tducret/programmateur-fil-pilote-wifi/Matériel/1.0/ProgrammateurFilPilote_1.0_Recto.png

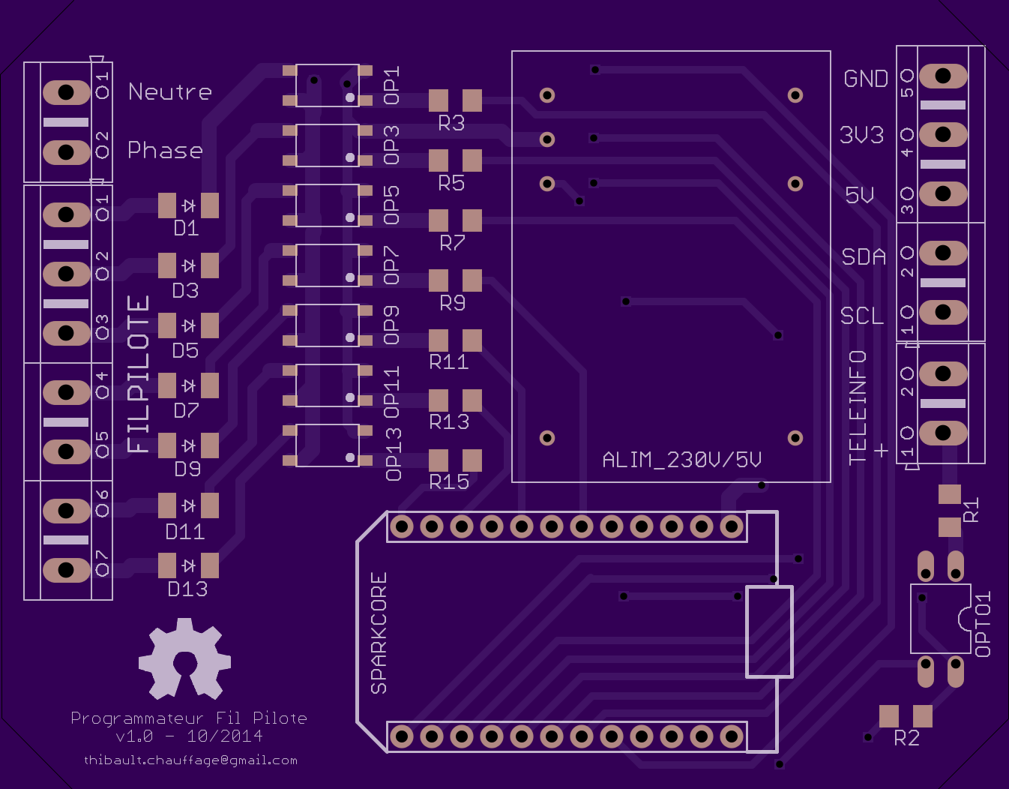
Matériel/1.0/ProgrammateurFilPilote_1.0_Recto.png
