tducret/programmateur-fil-pilote-wifi/Matériel/1.0/ProgrammateurFilPilote_1.0_Verso.png

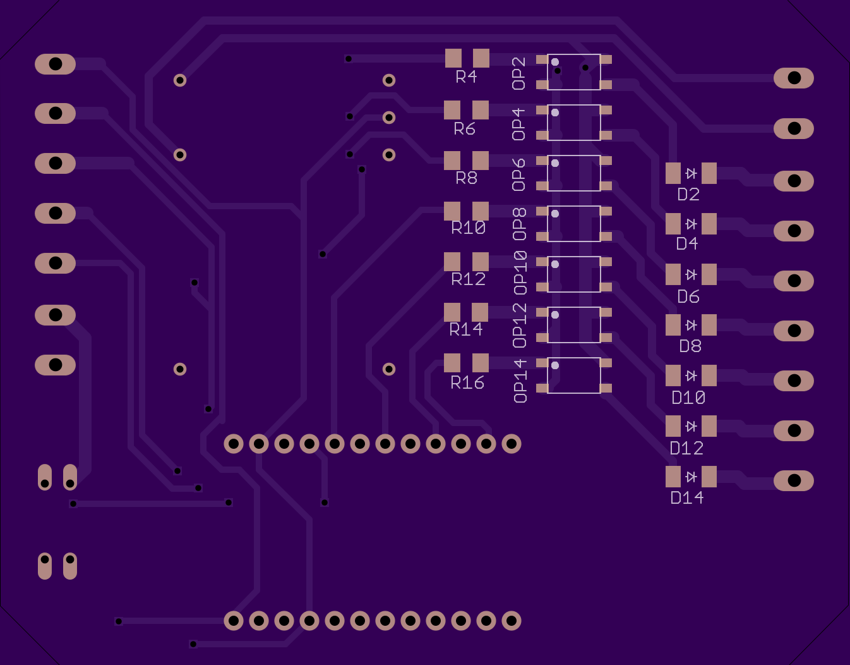
Matériel/1.0/ProgrammateurFilPilote_1.0_Verso.png
