tducret/programmateur-fil-pilote-wifi/Matériel/1.1.1/ProgrammateurFilPilote_1.1.1_Verso.png

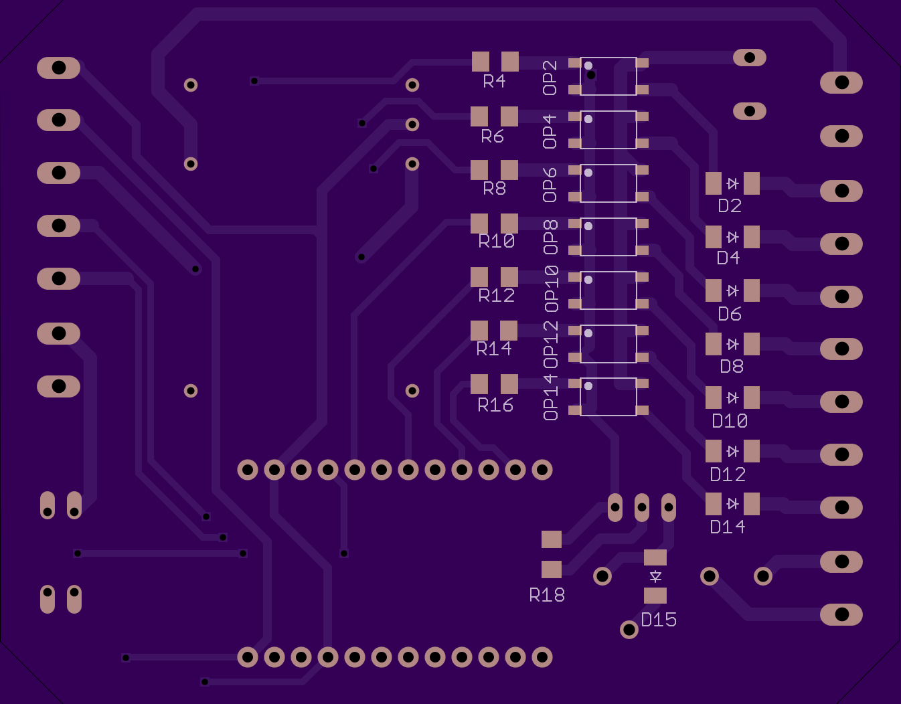
Matériel/1.1.1/ProgrammateurFilPilote_1.1.1_Verso.png
