tducret/programmateur-fil-pilote-wifi/Matériel/1.2/ProgrammateurFilPilote_1.2_Board.png

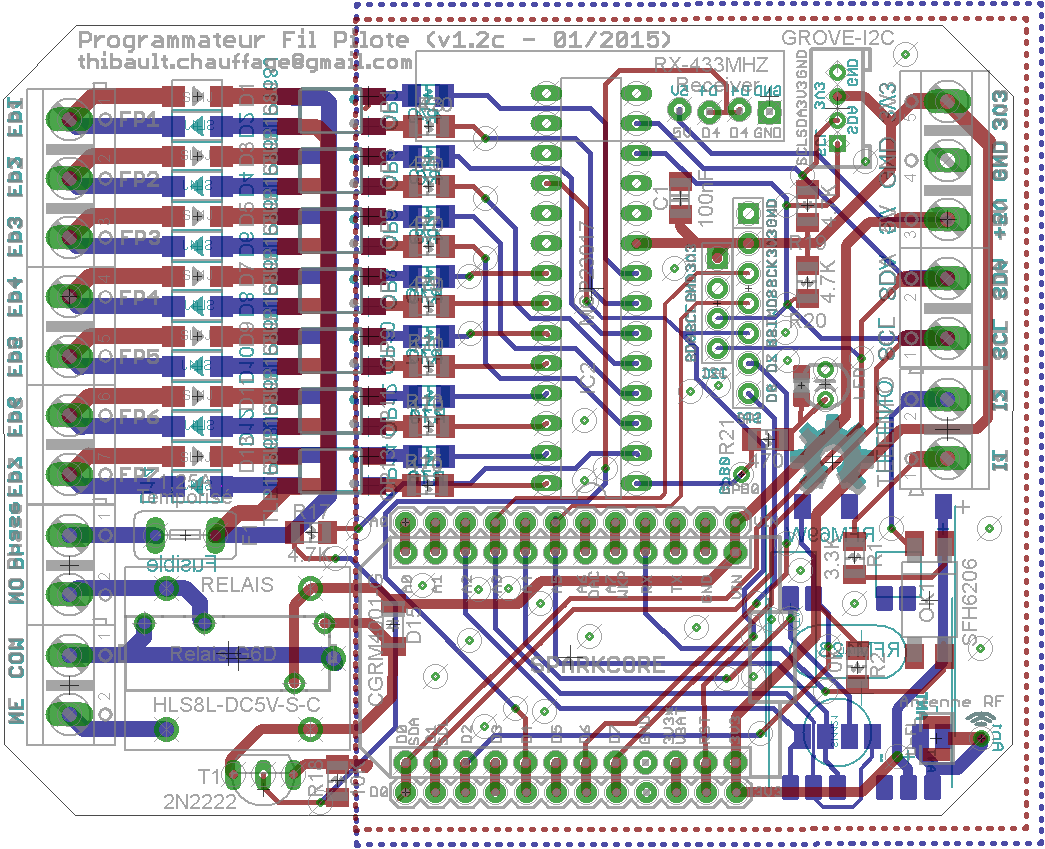
Matériel/1.2/ProgrammateurFilPilote_1.2_Board.png
