tducret/programmateur-fil-pilote-wifi/Matériel/1.2/ProgrammateurFilPilote_1.2_Recto.png

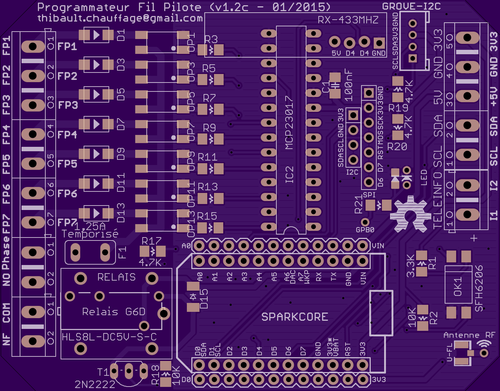
Matériel/1.2/ProgrammateurFilPilote_1.2_Recto.png
