tducret/programmateur-fil-pilote-wifi/Matériel/1.2/ProgrammateurFilPilote_1.2_Verso.png

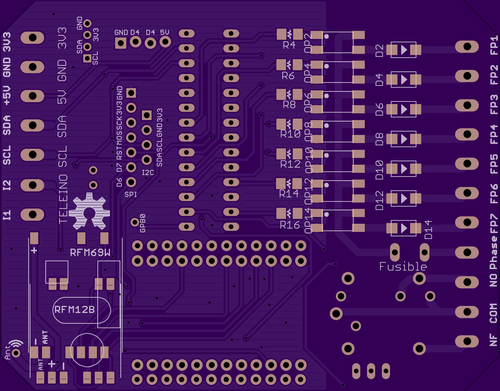
Matériel/1.2/ProgrammateurFilPilote_1.2_Verso.png
