tducret/programmateur-fil-pilote-wifi/Matériel/1.3/ProgrammateurFilPilote_1.3_Verso.png

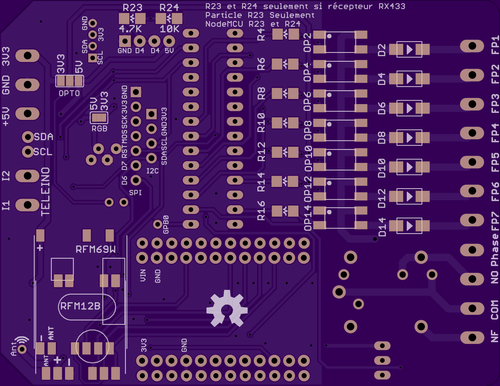
Matériel/1.3/ProgrammateurFilPilote_1.3_Verso.png
