tducret/programmateur-fil-pilote-wifi/Matériel/1.3/Tutoriel/Images/Photo16.jpeg

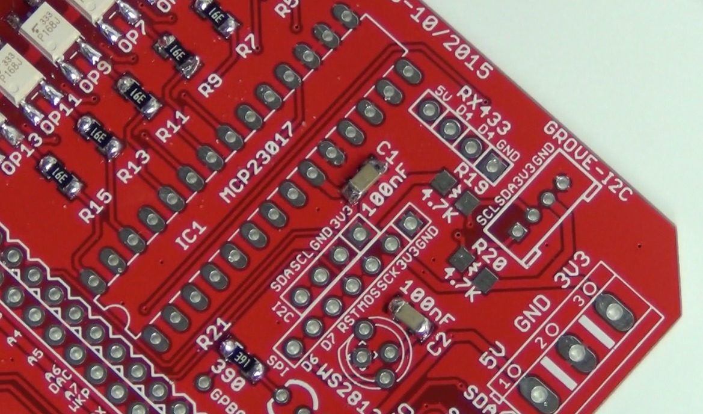
Matériel/1.3/Tutoriel/Images/Photo16.jpeg
