tducret/programmateur-fil-pilote-wifi/Logiciel/remora/WebServer/WebServer.h

/* -*- Mode: C++; tab-width: 2; indent-tabs-mode: nil;  c-file-style: "k&r"; c-basic-offset: 2; -*-

   Webduino, a simple Arduino web server
   Copyright 2009-2014 Ben Combee, Ran Talbott, Christopher Lee, Martin Lormes
   Francisco M Cuenca-Acuna, Matthew McGowan

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
   THE SOFTWARE IS PROVIDED "AS IS", WITHOUT WARRANTY OF ANY KIND, EXPRESS OR
   IMPLIED, INCLUDING BUT NOT LIMITED TO THE WARRANTIES OF MERCHANTABILITY,
   FITNESS FOR A PARTICULAR PURPOSE AND NONINFRINGEMENT. IN NO EVENT SHALL THE
   AUTHORS OR COPYRIGHT HOLDERS BE LIABLE FOR ANY CLAIM, DAMAGES OR OTHER
   LIABILITY, WHETHER IN AN ACTION OF CONTRACT, TORT OR OTHERWISE, ARISING FROM,
   OUT OF OR IN CONNECTION WITH THE SOFTWARE OR THE USE OR OTHER DEALINGS IN
   THE SOFTWARE.
*/

#ifndef WEBDUINO_H_
#define WEBDUINO_H_

#include <string.h>
#include <stdlib.h>
#include <stdarg.h>
#include "remora.h"

// TODO - this is necessary to avoid sockets being unexpectedly closed.
// https://community.spark.io/t/unwanted-but-reproducable-disconnect-in-tcpclient/5265
#define fixmedelay() delay(20)

/********************************************************************
 * CONFIGURATION
 ********************************************************************/

#define WEBDUINO_VERSION 1007
#define WEBDUINO_VERSION_STRING "1.7"

// standard END-OF-LINE marker in HTTP
#define CRLF "\r\n"

// If processConnection is called without a buffer, it allocates one
// of 32 bytes
#define WEBDUINO_DEFAULT_REQUEST_LENGTH 32

// How long to wait before considering a connection as dead when
// reading the HTTP request.  Used to avoid DOS attacks.
#ifndef WEBDUINO_READ_TIMEOUT_IN_MS
#define WEBDUINO_READ_TIMEOUT_IN_MS 1000
#endif

#ifndef WEBDUINO_COMMANDS_COUNT
#define WEBDUINO_COMMANDS_COUNT 8
#endif

#ifndef WEBDUINO_URL_PATH_COMMAND_LENGTH
#define WEBDUINO_URL_PATH_COMMAND_LENGTH 8
#endif

#ifndef WEBDUINO_FAIL_MESSAGE
#define WEBDUINO_FAIL_MESSAGE "<h1>EPIC FAIL</h1>"
#endif

#ifndef WEBDUINO_AUTH_REALM
#define WEBDUINO_AUTH_REALM "Webduino"
#endif // #ifndef WEBDUINO_AUTH_REALM

#ifndef WEBDUINO_AUTH_MESSAGE
#define WEBDUINO_AUTH_MESSAGE "<h1>401 Unauthorized</h1>"
#endif // #ifndef WEBDUINO_AUTH_MESSAGE

#ifndef WEBDUINO_SERVER_ERROR_MESSAGE
#define WEBDUINO_SERVER_ERROR_MESSAGE "<h1>500 Internal Server Error</h1>"
#endif // WEBDUINO_SERVER_ERROR_MESSAGE

#ifndef WEBDUINO_OUTPUT_BUFFER_SIZE
#define WEBDUINO_OUTPUT_BUFFER_SIZE 32
#endif // WEBDUINO_OUTPUT_BUFFER_SIZE

// add '#define WEBDUINO_FAVICON_DATA ""' to your application
// before including WebServer.h to send a null file as the favicon.ico file
// otherwise this defaults to a 16x16 px black diode on blue ground
// (or include your own icon if you like)
#ifndef WEBDUINO_FAVICON_DATA
#define WEBDUINO_FAVICON_DATA { 0x00, 0x00, 0x01, 0x00, 0x01, 0x00, 0x10, \
                                0x10, 0x02, 0x00, 0x01, 0x00, 0x01, 0x00, \
                                0xb0, 0x00, 0x00, 0x00, 0x16, 0x00, 0x00, \
                                0x00, 0x28, 0x00, 0x00, 0x00, 0x10, 0x00, \
                                0x00, 0x00, 0x20, 0x00, 0x00, 0x00, 0x01, \
                                0x00, 0x01, 0x00, 0x00, 0x00, 0x00, 0x00, \
                                0x00, 0x00, 0x00, 0x00, 0x00, 0x00, 0x00, \
                                0x00, 0x00, 0x00, 0x00, 0x00, 0x00, 0x00, \
                                0x00, 0x00, 0x00, 0x00, 0x00, 0x00, 0x00, \
                                0x00, 0x00, 0x00, 0xff, 0x00, 0x00, 0x00, \
                                0xff, 0xff, 0x00, 0x00, 0xff, 0xff, 0x00, \
                                0x00, 0xff, 0xff, 0x00, 0x00, 0xcf, 0xbf, \
                                0x00, 0x00, 0xc7, 0xbf, 0x00, 0x00, 0xc3, \
                                0xbf, 0x00, 0x00, 0xc1, 0xbf, 0x00, 0x00, \
                                0xc0, 0xbf, 0x00, 0x00, 0x00, 0x00, 0x00, \
                                0x00, 0xc0, 0xbf, 0x00, 0x00, 0xc1, 0xbf, \
                                0x00, 0x00, 0xc3, 0xbf, 0x00, 0x00, 0xc7, \
                                0xbf, 0x00, 0x00, 0xcf, 0xbf, 0x00, 0x00, \
                                0xff, 0xff, 0x00, 0x00, 0xff, 0xff, 0x00, \
                                0x00, 0x00, 0x00, 0x00, 0x00, 0x00, 0x00, \
                                0x00, 0x00, 0x00, 0x00, 0x00, 0x00, 0x00, \
                                0x00, 0x00, 0x00, 0x00, 0x00, 0x00, 0x00, \
                                0x00, 0x00, 0x00, 0x00, 0x00, 0x00, 0x00, \
                                0x00, 0x00, 0x00, 0x00, 0x00, 0x00, 0x00, \
                                0x00, 0x00, 0x00, 0x00, 0x00, 0x00, 0x00, \
                                0x00, 0x00, 0x00, 0x00, 0x00, 0x00, 0x00, \
                                0x00, 0x00, 0x00, 0x00, 0x00, 0x00, 0x00, \
                                0x00, 0x00, 0x00, 0x00, 0x00, 0x00, 0x00, \
                                0x00, 0x00 }
#endif // #ifndef WEBDUINO_FAVICON_DATA

// add "#define WEBDUINO_SERIAL_DEBUGGING 1" to your application
// before including WebServer.h to have incoming requests logged to
// the serial port.
#ifndef WEBDUINO_SERIAL_DEBUGGING
#define WEBDUINO_SERIAL_DEBUGGING 0
#endif
#if WEBDUINO_SERIAL_DEBUGGING
	#define SERIAL_DUMP(buf, len) Serial.write(buf, len);
#else
	#define SERIAL_DUMP(buf, len)
#endif

// declare a static string
#define P(name)   static const unsigned char name[]

// returns the number of elements in the array
#define SIZE(array) (sizeof(array) / sizeof(*array))

/********************************************************************
 * DECLARATIONS
 ********************************************************************/

/* Return codes from nextURLparam.  NOTE: URLPARAM_EOS is returned
 * when you call nextURLparam AFTER the last parameter is read.  The
 * last actual parameter gets an "OK" return code. */

enum URLPARAM_RESULT { URLPARAM_OK,
                       URLPARAM_NAME_OFLO,
                       URLPARAM_VALUE_OFLO,
                       URLPARAM_BOTH_OFLO,
                       URLPARAM_EOS         // No params left
};

class WebServer: public Print
{
public:
  // passed to a command to indicate what kind of request was received
  enum ConnectionType { INVALID, GET, HEAD, POST, PUT, DELETE, PATCH };

  // any commands registered with the web server have to follow
  // this prototype.
  // url_tail contains the part of the URL that wasn't matched against
  //          the registered command table.
  // tail_complete is true if the complete URL fit in url_tail,  false if
  //          part of it was lost because the buffer was too small.
  typedef void Command(WebServer &server, ConnectionType type,
                       char *url_tail, bool tail_complete);

  // Prototype for the optional function which consumes the URL path itself.
  // url_path contains pointers to the seperate parts of the URL path where '/'
  //          was used as the delimiter.
  typedef void UrlPathCommand(WebServer &server, ConnectionType type,
                              char **url_path, char *url_tail,
                              bool tail_complete);

  // constructor for webserver object
  WebServer(const char *urlPrefix = "", uint16_t port = 80);

  // start listening for connections
  void begin();

  // check for an incoming connection, and if it exists, process it
  // by reading its request and calling the appropriate command
  // handler.  This version is for compatibility with apps written for
  // version 1.1,  and allocates the URL "tail" buffer internally.
  void processConnection();

  // check for an incoming connection, and if it exists, process it
  // by reading its request and calling the appropriate command
  // handler.  This version saves the "tail" of the URL in buff.
  void processConnection(char *buff, int *bufflen);

  // set command that's run when you access the root of the server
  void setDefaultCommand(Command *cmd);

  // set command run for undefined pages
  void setFailureCommand(Command *cmd);

  // call from non-failure command handlers when they find they cannot handle a request
  void unhandledCommmand(ConnectionType requestType, char *verb, bool tail_complete);


  // add a new command to be run at the URL specified by verb
  void addCommand(const char *verb, Command *cmd);

  // Set command that's run if default command or URL specified commands do
  // not run, uses extra url_path parameter to allow resolving the URL in the
  // function.
  void setUrlPathCommand(UrlPathCommand *cmd);

  // utility function to output CRLF pair
  void printCRLF();

  // output a string stored in program memory, usually one defined
  // with the P macro
  void printP(const unsigned char *str);

  // inline overload for printP to handle signed char strings
  void printP(const char *str) { printP((unsigned char*)str); }

  // support for C style formating
  void printf(char *fmt, ... );
  #ifdef F
  void printf(const __FlashStringHelper *format, ... );
  #endif

  // output raw data stored in program memory
  void writeP(const unsigned char *data, size_t length);

  // output HTML for a radio button
  void radioButton(const char *name, const char *val,
                   const char *label, bool selected);

  // output HTML for a checkbox
  void checkBox(const char *name, const char *val,
                const char *label, bool selected);

  // returns next character or -1 if we're at end-of-stream
  int read();

  // put a character that's been read back into the input pool
  void push(int ch);

  // returns true if the string is next in the stream.  Doesn't
  // consume any character if false, so can be used to try out
  // different expected values.
  bool expect(const char *expectedStr);

  // returns true if a number, with possible whitespace in front, was
  // read from the server stream.  number will be set with the new
  // value or 0 if nothing was read.
  bool readInt(int &number);

  // reads a header value, stripped of possible whitespace in front,
  // from the server stream
  void readHeader(char *value, int valueLen);

  // Read the next keyword parameter from the socket.  Assumes that other
  // code has already skipped over the headers,  and the next thing to
  // be read will be the start of a keyword.
  //
  // returns true if we're not at end-of-stream
  bool readPOSTparam(char *name, int nameLen, char *value, int valueLen);

  // Read the next keyword parameter from the buffer filled by getRequest.
  //
  // returns 0 if everything weent okay,  non-zero if not
  // (see the typedef for codes)
  URLPARAM_RESULT nextURLparam(char **tail, char *name, int nameLen,
                               char *value, int valueLen);

  // compare string against credentials in current request
  //
  // authCredentials must be Base64 encoded outside of Webduino
  // (I wanted to be easy on the resources)
  //
  // returns true if strings match, false otherwise
  bool checkCredentials(const char authCredentials[45]);

  // output headers and a message indicating a server error
  void httpFail();

  // output headers and a message indicating "401 Unauthorized"
  void httpUnauthorized();

  // output headers and a message indicating "500 Internal Server Error"
  void httpServerError();

  // output headers indicating "204 No Content" and no further message
  void httpNoContent();

  // output standard headers indicating "200 Success".  You can change the
  // type of the data you're outputting or also add extra headers like
  // "Refresh: 1".  Extra headers should each be terminated with CRLF.
  void httpSuccess(const char *contentType = "text/html; charset=utf-8",
                   const char *extraHeaders = NULL);

  // used with POST to output a redirect to another URL.  This is
  // preferable to outputting HTML from a post because you can then
  // refresh the page without getting a "resubmit form" dialog.
  void httpSeeOther(const char *otherURL);

  // implementation of write used to implement Print interface
  virtual size_t write(uint8_t);
  virtual size_t write(const uint8_t *buffer, size_t size);

  // tells if there is anything to process
  uint8_t available();

  // Flush the send buffer
  void flushBuf();

  // Close the current connection and flush ethernet buffers
  void reset();


private:

  TCPServer m_server;
  TCPClient m_client;

  const char *m_urlPrefix;

  unsigned char m_pushback[32];
  unsigned char m_pushbackDepth;

  int m_contentLength;
  char m_authCredentials[51];
  bool m_readingContent;

  Command *m_failureCmd;
  Command *m_defaultCmd;
  struct CommandMap
  {
    const char *verb;
    Command *cmd;
  } m_commands[WEBDUINO_COMMANDS_COUNT];

  unsigned char m_cmdCount;
  UrlPathCommand *m_urlPathCmd;

  uint8_t m_buffer[WEBDUINO_OUTPUT_BUFFER_SIZE];
  uint8_t m_bufFill;

  void getRequest(WebServer::ConnectionType &type, char *request, int *length);
  bool dispatchCommand(ConnectionType requestType, char *verb, bool tail_complete);
  void processHeaders();
  void outputCheckboxOrRadio(const char *element, const char *name, const char *val, const char *label, bool selected);
  static void defaultFailCmd(WebServer &server, ConnectionType type, char *url_tail, bool tail_complete);
  void noRobots(ConnectionType type);
  void favicon(ConnectionType type);
};

#endif // WEBDUINO_H_
