tducret/programmateur-fil-pilote-wifi/Logiciel/remora/rfm.cpp

// **********************************************************************************
// RFM69 module management source file for remora project
// **********************************************************************************
// Creative Commons Attrib Share-Alike License
// You are free to use/extend but please abide with the CC-BY-SA license:
// http://creativecommons.org/licenses/by-sa/4.0/
//
// Written by Charles-Henri Hallard (http://hallard.me)
//
// History : V1.00 2015-01-22 - First release
//
// All text above must be included in any redistribution.
//
// **********************************************************************************

#include "./linked_list.h"
#include "./ULPNode_RF_Protocol.h"
#include "./rfm.h"
#include "./RH_RF69.h"


unsigned long rf_rgb_led_timer = 0;

// data received by RF module
// independent from module received (RF12 or RF69)
// used to display or send to serial
RFData data;

// Linked list of nodes seens
NodeList nodes_list;

// RadioHead Library need driver and message class
//RH_RF69     rf69_drv(RF69_CS, RF69_IRQ);// instance of the radio driver
//RHDatagram  rf69(rf69_drv);         // Manage message delivery and receipt
//RH_RF69 * prf69_drv = &rf69_drv;
#ifdef ESP8266
  #ifdef RH_RF69_IRQLESS
    RH_RF69 driver(RF69_CS, RF69_IRQ);// instance of the radio driver
  #else
    // instance of the radio driver we can't use GPPIO2
    RH_RF69 driver(RF69_IRQ, RF69_CS);
  #endif
#else
  // instance of the radio driver
  RH_RF69 driver(RF69_CS, RF69_IRQ);
#endif

/* ======================================================================
Function: rfm_receive_data
Purpose : receive data payload on RF and manage ACK
Input   : -
Output  : millis since this node has been seen
Comments: called from loop, this is a non blocking receiver
====================================================================== */
unsigned long rfm_receive_data(void)
{
  unsigned long node_last_seen = 0;

  LedRGBON(COLOR_BLUE);
  rf_rgb_led_timer = millis();

  // Fill known values
  data.size    = sizeof(data.buffer);
  data.groupid = RFM69_NETWORKID;
  data.ack = '\0';  // default no ack

  // grab the frame received
  if (driver.recv(data.buffer, &data.size)) {
    bool  known_node = false;
    int   nb_node;
    int   current;
    uint8_t toid;

    // Get header data
    data.nodeid = driver.headerFrom();
    toid        = driver.headerTo();
    data.seqid  = driver.headerId();
    data.flags  = driver.headerFlags();
    data.rssi   = driver.lastRssi();

    // Are we authorized to send response ?
    // This is in case of multiple gateways with same ID
    //if (!(config.mode & CFG_RF69_NOSEND)) {
    if (true) {
      // Sender explicitly requested a ACK ?
      if (data.flags & RF_PAYLOAD_REQ_ACK) {
        //DebugF("Frame from ");
        //Debug(data.nodeid);
        //DebugF(" to ");
        //Debug(toid);
        //DebugF(" want ACK ");

        // Never ACK on broadcast address or a already ACK response
        if (toid!=RH_BROADCAST_ADDRESS && !(data.flags & RH_FLAGS_ACK)) {
          //DebugF("Me=");
          //Debug(toid);
          //DebugF(" Sending ACK to ");
          //Debug(data.nodeid);

          // Header is now ACK response (set) and no more ACK Request (clear)
          driver.setHeaderFlags(RH_FLAGS_ACK, RF_PAYLOAD_REQ_ACK);
          driver.setHeaderId(data.seqid);
          driver.setHeaderTo(data.nodeid);
          driver.setHeaderFrom(toid);
          data.ack = '!';

          // We have powerfull speed CPU, but Wait slave to setup the receiver for
          // ACK reception
          #if (RF_GATEWAY_PLATFORM==RF_GATEWAY_PLATFORM_PARTICLE) || defined (ESP8266)
            delay(1);
            //delayMicroseconds(100);
          #endif

          // Send the response packet
          driver.send(&data.ack, sizeof(data.ack));
          driver.waitPacketSent();

          // ACK makes led to green
          #if defined (RGB_LED_PIN)
            LedRGBON(0,COLOR_GREEN);
          #endif

        }
      }
    }
    // Prepare our last seen value
    node_last_seen = uptime;

    ll_Add(&nodes_list, data.groupid, data.nodeid, data.rssi, &node_last_seen);
    //ll_Dump(&nodes_list, g_second);

  } // revcfrom()

  return node_last_seen;
}


/* ======================================================================
Function: rfm_setup
Purpose : prepare and init stuff, configuration, ..
Input   : -
Output  : true if RF module found, false otherwise
Comments: -
====================================================================== */
bool rfm_setup(void)
{
  bool ret = false;

  Serial.print("Initializing RFM69...");
  Serial.flush();

  // RF Radio initialization
  // =======================
  // Defaults after RadioHead init are
  // 434.0MHz
  // modulation GFSK_Rb250Fd250, +13dbM
  // No encryption
  if (!driver.init()) {
    Serial.println("Not found!");
  } else {
    Serial.println("OK!");

    // If you are using a high power RF69, you *must* set a Tx power in the
    // range 14 to 20 like this:
    driver.setTxPower(20);

    // set driver parameters
    driver.setThisAddress(RFM69_NODEID);  // filtering address when receiving
    driver.setHeaderFrom(RFM69_NODEID);   // Transmit From Node

    // Init of our linked list of seen received nodes
    nodes_list.next     = NULL ;
    nodes_list.groupid  = 0 ;
    nodes_list.nodeid   = 0 ;
    nodes_list.rssi     = 0 ;
    nodes_list.lastseen = 0 ;
  }

  Serial.flush();
  return (ret);

}

/* ======================================================================
Function: rfm_loop
Purpose : really need to tell ?
Input   : -
Output  : -
Comments: -
====================================================================== */
void rfm_loop(void)
{

  static uint8_t got_first = false;
  static unsigned long packet_last_seen=0;// second since last packet received
  uint8_t packetReceived = 0;
  unsigned long node_last_seen;  // Second since we saw this node
  unsigned long currentMillis = millis();

  // Data received from driver ?
  if (driver.available()) {
    node_last_seen = rfm_receive_data();
    packet_last_seen = uptime;
    packetReceived = true;
  }

  // received data ?
  if (packetReceived) {
    // command code
    uint8_t cmd = data.buffer[0];
    unsigned long seen = uptime-node_last_seen;

    #define DEBUG_VERBOSE
    #ifdef DEBUG_VERBOSE
      // Dump Raw packet
      Serial.print(F("# ("));
      Serial.print(uptime);
      Serial.print(F(")"));

      if (data.flags & RF_PAYLOAD_REQ_ACK)
        Serial.print(F(" ACKED"));


      Serial.print(F(" <- node:"));  Serial.print(data.nodeid,DEC);
      Serial.print(F(" size:"));     Serial.print(data.size);
      Serial.print(F(" type:"));     Serial.print(decode_frame_type(cmd));
      Serial.print(F(" (0x"));       Serial.print(cmd,HEX);
      Serial.print(F(") RSSI:"));    Serial.print(data.rssi,DEC);
      Serial.print(F("dB  seen :"));
      Serial.print(timeAgo(seen));

      // Detail to know exactly number of seconds between node send
      if ( seen<=300 && seen>0 ) {
        Serial.print(F(" ("));
        Serial.print(seen);
        Serial.print(F(")"));
      }

      Serial.print(F("\r\n# buffer:"));

      char buff[4];
      for (uint8_t i=0; i<data.size; i++) {
        sprintf_P(buff, PSTR(" %02X"), data.buffer[i]);
        Serial.print(buff);
      }

      Serial.print(F("  "));
      #ifdef SPARK
        Serial.print(System.freeMemory());
      #else
        Serial.print(ESP.getFreeHeap());
      #endif
      Serial.println(F(" Bytes free "));
    #endif

    // decode format
    // return command code validated by payload type size received
    // so if we had a command and the payload does not match
    // code as been set to 0 by decode_received_data
    cmd = decode_received_data(data.nodeid, data.rssi, data.size, cmd, data.buffer);

   // special ping packet, we need to answer back
   if ( cmd==RF_PL_PING ) {
     RFPingPayload * ppl = (RFPingPayload *) data.buffer;

     // prepare send back response
     ppl->command = RF_PL_PINGBACK;
     ppl->vbat = 0;
     ppl->rssi = data.rssi; // RSSI of node
     ppl->status = 0;

     driver.setHeaderId(data.seqid);
     driver.setHeaderFlags(RH_FLAGS_NONE);

     // We're on a fast gateway, let node some time
     // To node to set to receive mode before sending response
     delay(2);
     driver.setHeaderTo(data.nodeid);
     driver.send((uint8_t *) ppl, (uint8_t) sizeof(RFPingPayload)) ;
     driver.waitPacketSent();

     // Start line with a # (comment)
     // indicate external parser that it's just debug information
     Serial.print(F("\r\n# -> "));
     Serial.print(data.nodeid,DEC);
     Serial.print(F(" PINGBACK ("));
     Serial.print(ppl->rssi,DEC);
     Serial.println(F("dB)"));
   }

   // Start blue led
   LedRGBON(COLOR_BLUE);
   rf_rgb_led_timer=millis();

   // known Payload ? send frame to serial
   if (cmd) {
     Serial.println(json_str);
   }


   // Display Results only if something new received
   // As display on OLED is quite long, this avoid time out
   // on ack of RF module because if we are in display, we can't
   // ACK quickly and may be delayed by 100ms, but if we are
   // there this is because we received a command and treated ACK
   //#ifdef MOD_LCD
  //   screen_state = screen_rf;
  //   doDisplay();
  // #endif

  }

  // Do we have led timer expiration ?
  if (rf_rgb_led_timer && (millis()-rf_rgb_led_timer >= RF_LED_BLINK_MS)) {
   LedRGBOFF();     // Light Off the LED
   rf_rgb_led_timer=0; // Stop virtual timer
  }

}
